PelionIoT/ref-wem-hardware/images/earwig-01.png

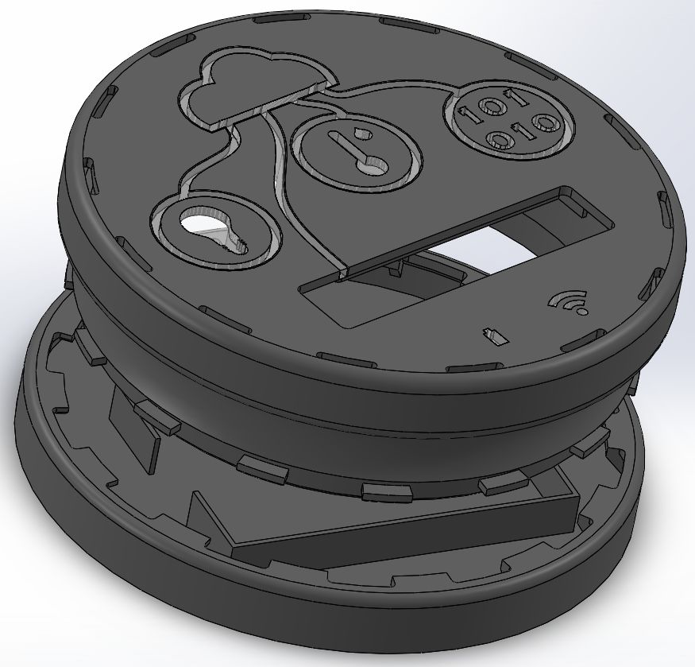
images/earwig-01.png
