PelionIoT/ref-wem-hardware/images/earwig-07.png

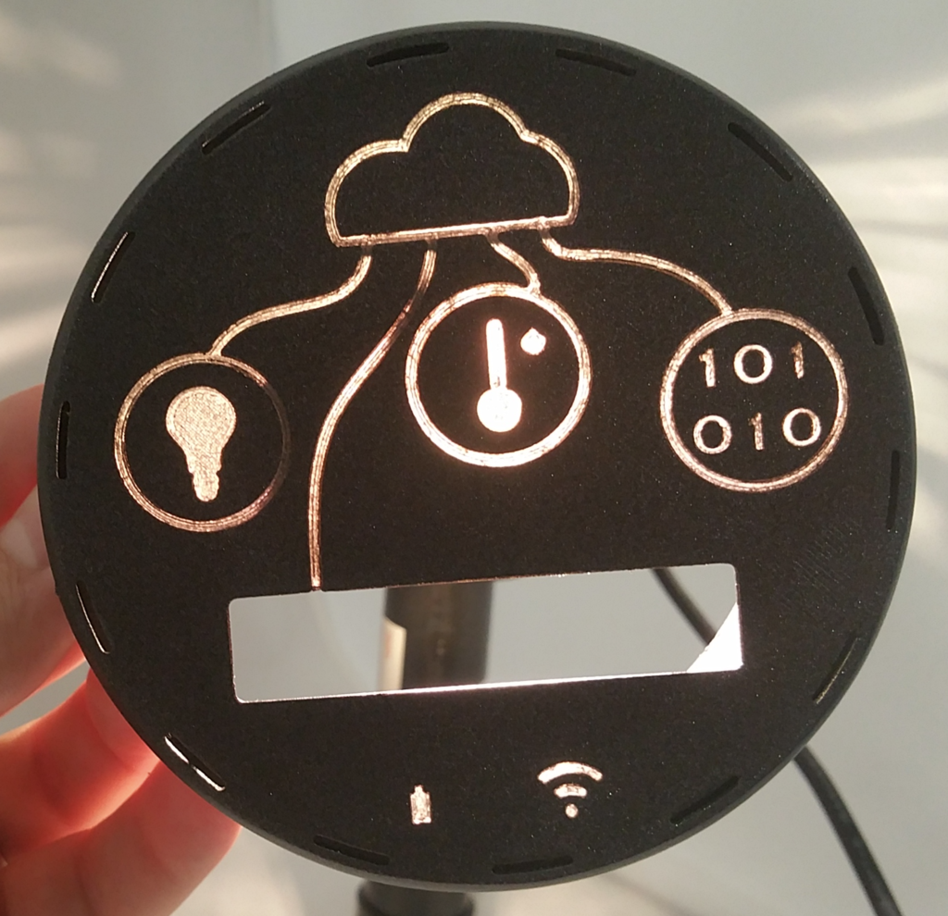
images/earwig-07.png
