PelionIoT/ref-wem-hardware/images/image2017-12-12_12-43-38.png

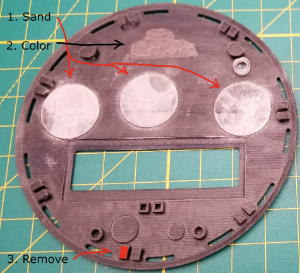
images/image2017-12-12_12-43-38.png
