PelionIoT/ref-wem-hardware/images/image2017-12-12_12-53-47.png

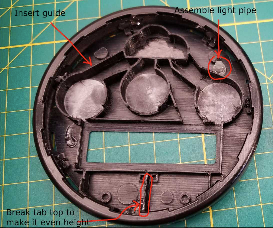
images/image2017-12-12_12-53-47.png
