PelionIoT/ref-wem-hardware/images/image2017-12-12_13-11-30.png

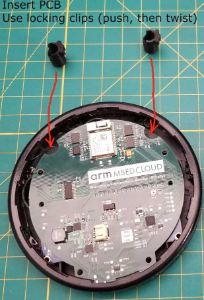
images/image2017-12-12_13-11-30.png
