PelionIoT/ref-wem-hardware/images/image2017-12-12_13-12-17.png

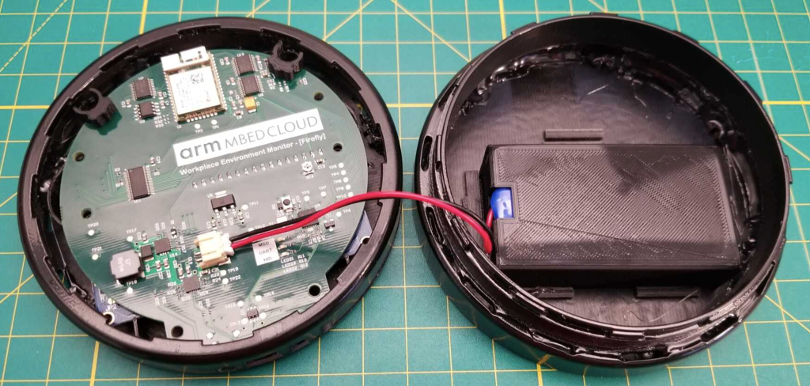
images/image2017-12-12_13-12-17.png
