PelionIoT/ref-wem-hardware/CAD/Enclosure slide clip.sldprt

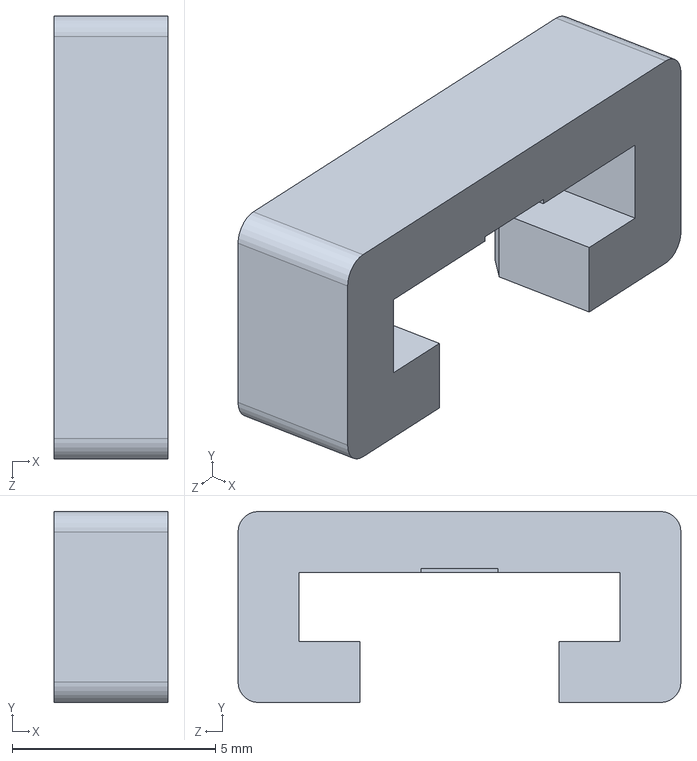
[picture p27: CAD file, 2018-03-06]
CAD/Enclosure slide clip.sldprt
2.80 x 4.70 x 10.9 mm
